p4nic4ttack/diy-tamagotchi/pictures/sleeping.png

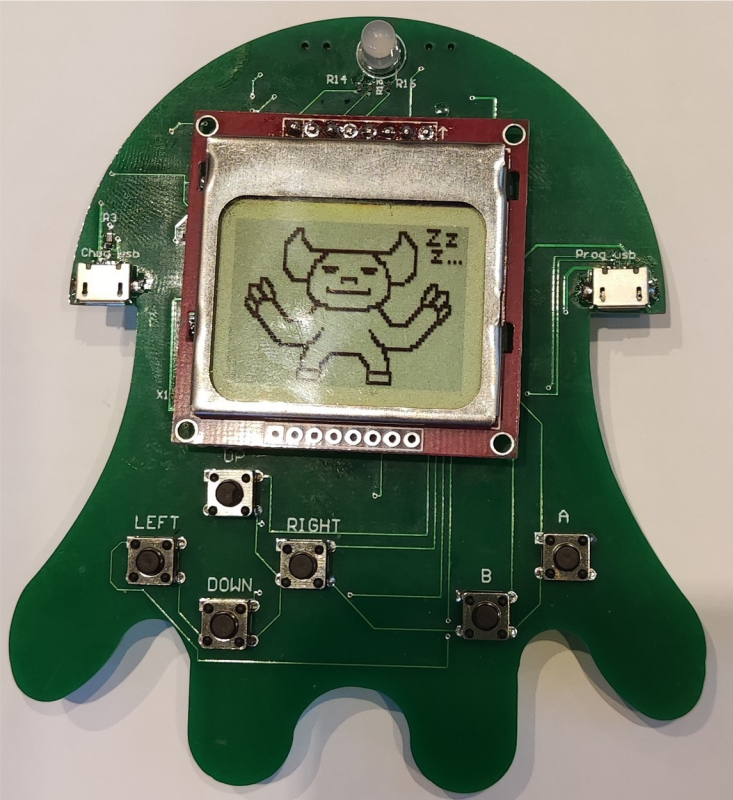
pictures/sleeping.png
