p4nic4ttack/diy-tamagotchi/chars.h

#ifndef CHARS_H
#define CHARS_H
typedef struct Pair{
	int idx;
	uint8_t new_byte;
} Pair; 

static const uint8_t ascii[] = {
0x00, 0x00, 0x00, 0x00, 0x00, 0x00,
0x00, 0x00, 0x5f, 0x00, 0x00, 0x00,
0x00, 0x07, 0x00, 0x07, 0x00, 0x00,
0x14, 0x7f, 0x14, 0x7f, 0x14, 0x00,
0x24, 0x2a, 0x7f, 0x2a, 0x12, 0x00,
0x23, 0x13, 0x08, 0x64, 0x62, 0x00,
0x36, 0x49, 0x55, 0x22, 0x50, 0x00,
0x00, 0x05, 0x03, 0x00, 0x00, 0x00,
0x00, 0x1c, 0x22, 0x41, 0x00, 0x00,
0x00, 0x41, 0x22, 0x1c, 0x00, 0x00,
0x14, 0x08, 0x3e, 0x08, 0x14, 0x00,
0x08, 0x08, 0x3e, 0x08, 0x08, 0x00,
0x00, 0x50, 0x30, 0x00, 0x00, 0x00,
0x08, 0x08, 0x08, 0x08, 0x08, 0x00,
0x00, 0x60, 0x60, 0x00, 0x00, 0x00,
0x20, 0x10, 0x08, 0x04, 0x02, 0x00,
0x3e, 0x51, 0x49, 0x45, 0x3e, 0x00,
0x00, 0x42, 0x7f, 0x40, 0x00, 0x00,
0x42, 0x61, 0x51, 0x49, 0x46, 0x00,
0x21, 0x41, 0x45, 0x4b, 0x31, 0x00,
0x18, 0x14, 0x12, 0x7f, 0x10, 0x00,
0x27, 0x45, 0x45, 0x45, 0x39, 0x00,
0x3c, 0x4a, 0x49, 0x49, 0x30, 0x00,
0x01, 0x71, 0x09, 0x05, 0x03, 0x00,
0x36, 0x49, 0x49, 0x49, 0x36, 0x00,
0x06, 0x49, 0x49, 0x29, 0x1e, 0x00,
0x00, 0x36, 0x36, 0x00, 0x00, 0x00,
0x00, 0x56, 0x36, 0x00, 0x00, 0x00,
0x08, 0x14, 0x22, 0x41, 0x00, 0x00,
0x14, 0x14, 0x14, 0x14, 0x14, 0x00,
0x00, 0x41, 0x22, 0x14, 0x08, 0x00,
0x02, 0x01, 0x51, 0x09, 0x06, 0x00,
0x32, 0x49, 0x79, 0x41, 0x3e, 0x00,
0x7e, 0x11, 0x11, 0x11, 0x7e, 0x00,
0x7f, 0x49, 0x49, 0x49, 0x36, 0x00,
0x3e, 0x41, 0x41, 0x41, 0x22, 0x00,
0x7f, 0x41, 0x41, 0x22, 0x1c, 0x00,
0x7f, 0x49, 0x49, 0x49, 0x41, 0x00,
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
0x00, 0x00, 0x00, 0x00, 0x00, 0x00, 0x00, 0x00, 0x00, 0x00, 0x00, 0x00, 0x00, 0x78, 0x4F, 0x48,
0x48, 0x48, 0x48, 0x48, 0x48, 0x7E, 0x03, 0x01, 0x00, 0x00, 0x00, 0x00, 0x00, 0x00, 0x00, 0x00,
0x00, 0x00, 0x00, 0x00, 0x01, 0x03, 0x7E, 0x48, 0x48, 0x48, 0x48, 0x48, 0x48, 0x4F, 0x78, 0x00,
0x00, 0x00, 0x00, 0x00, 0x00, 0x00, 0x00, 0x00, 0x00, 0x00, 0x00, 0x00, 0x00, 0x00, 0x00, 0x00,
0x00, 0x00, 0x00, 0x00, 0x00, 0x00, 0x00, 0x00
};

//static const uint8_t alien1_evo[] = {0x00, 0x00, 0x00, 0x00, 0x00, 0x00, 0x00, 0x00, 0xe0, 0x30, 0x18, 0x08, 0xe8, 0xb8, 0x08, 0x00, 0x00, 0x00, 0x00, 0x00, 0x00, 0x00, 0x00, 0x80, 0xc0, 0x40, 0x60, 0x20, 0x20, 0x20, 0x60, 0x40, 0xc0, 0x80, 0x00, 0x00, 0x00, 0x80, 0xc0, 0x60, 0x30, 0x18, 0x18, 0x30, 0x60, 0xc0, 0x80, 0x00, 0x00, 0x00, 0x80, 0xc0, 0x40, 0x60, 0x20, 0x20, 0x20, 0x60, 0x40, 0xc0, 0x80, 0x00, 0x00, 0x00, 0x00, 0x00, 0x00, 0x00, 0x00, 0x08, 0xb8, 0xe8, 0x08, 0x18, 0x30, 0xe0, 0x00, 0x00, 0x00, 0x00, 0x00, 0x00, 0x00, 0x00, 0x00, 0x00, 0x00, 0x00, 0x00, 0x00, 0x00, 0x00, 0x0f, 0x18, 0x30, 0x60, 0xc0, 0x81, 0x03, 0x02, 0x02, 0x02, 0x02, 0x02, 0x03, 0x01, 0x01, 0x01, 0x00, 0x00, 0x00, 0x80, 0xe0, 0x30, 0x18, 0x0c, 0xe6, 0xb3, 0x19, 0x49, 0x19, 0xb3, 0xe5, 0x09, 0x11, 0x01, 0x01, 0x11, 0x09, 0xe5, 0xb3, 0x19, 0x49, 0x19, 0xb3, 0xe6, 0x0c, 0x18, 0x30, 0xe0, 0x80, 0x00, 0x00, 0x00, 0x01, 0x01, 0x01, 0x03, 0x02, 0x02, 0x02, 0x02, 0x02, 0x03, 0x81, 0xc0, 0x60, 0x30, 0x18, 0x0f, 0x00, 0x00, 0x00, 0x00, 0x00, 0x00, 0x00, 0x00, 0x00, 0x00, 0x00, 0x00, 0x00, 0x00, 0xf8, 0x18, 0x30, 0x60, 0xc0, 0x80, 0x00, 0x01, 0x03, 0x02, 0x02, 0x06, 0x84, 0x84, 0xc4, 0x44, 0x44, 0x4c, 0x48, 0x48, 0x48, 0x7f, 0x60, 0xc0, 0x80, 0x80, 0x00, 0x01, 0x1b, 0xf2, 0xb3, 0xf1, 0x70, 0xf3, 0xf5, 0xf1, 0xf1, 0xf5, 0xf3, 0x70, 0xf1, 0xb3, 0xf2, 0x1b, 0x01, 0x00, 0x80, 0x80, 0xc0, 0x60, 0x7f, 0x48, 0x48, 0x48, 0x4c, 0x44, 0x44, 0xc4, 0x84, 0x84, 0x06, 0x02, 0x02, 0x03, 0x01, 0x00, 0x80, 0xc0, 0x60, 0x3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
0x5D, 0x5D, 0x5D, 0x5D, 0x5D, 0x5D, 0x5D, 0x5D, 0x41, 0x41, 
0x5D, 0x5D, 0x5D, 0x5D, 0x5D, 0x5D, 0x5D, 0x5D, 0x5D, 0x5D, 
0x5D, 0x5D, 0x5D, 0x5D, 0x5D, 0x5D, 0x5D, 0x5D, 0x5D, 0x5D, 
0x41, 0x7F, 0x3E, 0x1C, 0x08, 0x00, 0x00, 0x00, 0x00, 0x00, 
0x00, 0x00, 0x00, 0x00
};

static const Pair neutral_health[] = {{50,0x41},{51,0x41},{52,0x41},{53,0x41},{54,0x41},{55,0x41},{56,0x41},{57,0x41},{58,0x41},{59,0x41},{60,0x41},{61,0x41},{62,0x41},{63,0x41},{64,0x41},{65,0x41},{66,0x41},{67,0x41},{68,0x41},{69,0x41}};
static const Pair sad_health[] = {{28,0x41},{29,0x41},{30,0x41},{31,0x41},{32,0x41},{33,0x41},{34,0x41},{35,0x41},{36,0x41},{37,0x41},{38,0x41},{39,0x41},{40,0x41},{41,0x41},{42,0x41},{43,0x41},{44,0x41},{45,0x41},{46,0x41},{47,0x41},{50,0x41},{51,0x41},{52,0x41},{53,0x41},{54,0x41},{55,0x41},{56,0x41},{57,0x41},{58,0x41},{59,0x41},{60,0x41},{61,0x41},{62,0x41},{63,0x41},{64,0x41},{65,0x41},{66,0x41},{67,0x41},{68,0x41},{69,0x41}};

static const uint8_t alien2[] = {0x00, 0x00, 0x00, 0x00, 0x00, 0x00, 0x00, 0x00, 0x00, 0x00, 0x00, 0x00, 0x00, 0x00, 0x00, 0x00, 0x00, 0x00, 0x00, 0x00, 0x00, 0x00, 0x00, 0x00, 0x00, 0x00, 0x80, 0xC0, 0x60, 0x30, 0x18, 0x88, 0x88, 0x88, 0x88, 0xC8, 0x88, 0x88, 0x98, 0xB0, 0xE0, 0xC0, 0x80, 0x80, 0xC0, 0xE0, 0xB0, 0x98, 0x88, 0x88, 0xC8, 0x88, 0x88, 0x88, 0x88, 0x18, 0x30, 0x60, 0xC0, 0x80, 0x00, 0x00, 0x00, 0x00, 0x00, 0x00, 0x00, 0x00, 0x00, 0x00, 0x00, 0x00, 0x00, 0x00, 0x00, 0x00, 0x00, 0x00, 0x00, 0x00, 0x00, 0x00, 0x00, 0x00, 0x00, 0x00, 0x00, 0x00, 0x00, 0x00, 0x00, 0x00, 0x00, 0x00, 0x00, 0x00, 0x00, 0x00, 0x00, 0x00, 0x00, 0x00, 0x00, 0x00, 0x00, 0x00, 0x00, 0x00, 0x00, 0x00, 0x01, 0x03, 0x06, 0x0C, 0x18, 0x10, 0x10, 0x11, 0x10, 0x10, 0x10, 0x11, 0x18, 0x0C, 0x07, 0xFF, 0x00, 0x00, 0xFF, 0x07, 0x0C, 0x18, 0x11, 0x10, 0x10, 0x10, 0x11, 0x10, 0x10, 0x18, 0x0C, 0x06, 0x03, 0x01, 0x00, 0x00, 0x00, 0x00, 0x00, 0x00, 0x00, 0x00, 0x00, 0x00, 0x00, 0x00, 0x00, 0x00, 0x00, 0x00, 0x00, 0x00, 0x00, 0x00, 0x00, 0x00, 0x00, 0x00, 0x00, 0x00, 0x00, 0x00, 0x00, 0x00, 0x00, 0x00, 0x00, 0x00, 0x00, 0x00, 0x00, 0x00, 0x00, 0x00, 0x00, 0x00, 0x00, 0x00, 0x00, 0x00, 0x00, 0x00, 0x00, 0x00, 0x00, 0x00, 0x00, 0x00, 0x00, 0x00, 0x00, 0x00, 0x00, 0x00, 0x00, 0x00, 0xC0, 0x7C, 0x04, 0x0F, 0x08, 0x08, 0x0F, 0x04, 0x7C, 0xC0, 0x00, 0x00, 0x00, 0x00, 0x00, 0x00, 0x00, 0x00, 0x00, 0x00, 0x00, 0x00, 0x00, 0x00, 0x00, 0x00, 0x00, 0x00, 0x00, 0x00, 0x00, 0x00, 0x00, 0x00, 0x00, 0x00, 0x00, 0x00, 0x0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
#endif
