p4nic4ttack/diy-tamagotchi/include/games.h

#ifndef GAMES_H
#define GAMES_H

#include <lcd.h>
#include <character.h>
#include <chars.h>
#include <rtc.h>
#include <buttons.h>
#include <rtc.h>
#include <stdlib.h>

uint8_t move_game(Tamagotchi*);

#endif
