p4nic4ttack/diy-tamagotchi/include/led.h

#ifndef LED_H
#define LED_H
#include <stdint.h>
void red(void);
void green(void);
void blue(void);
void clear_led(void);
void clear_red(void);
void clear_green(void);
void clear_blue(void);
void setcolor(uint8_t,uint8_t,uint8_t);


#endif
